Cardansan/CarritoFPV-v1/Piezas Impresión 3D/Imprimir Negro/14.STL

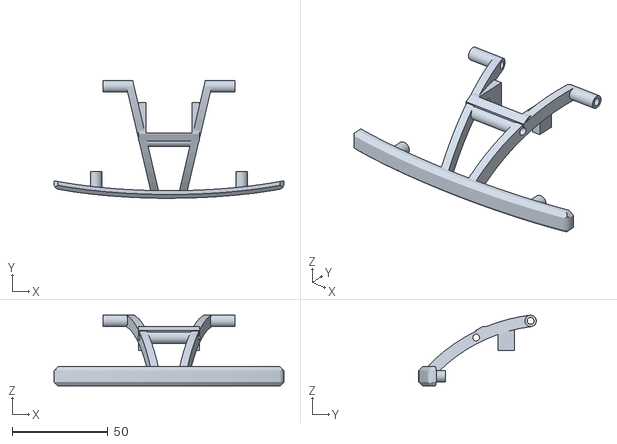
[picture p15: CAD file, 2019-08-24]
Piezas Impresión 3D/Imprimir Negro/14.STL
120.0 x 61.4 x 36.9
