Cardansan/CarritoFPV-v1/Piezas Impresión 3D/Imprimir Negro/9.STL

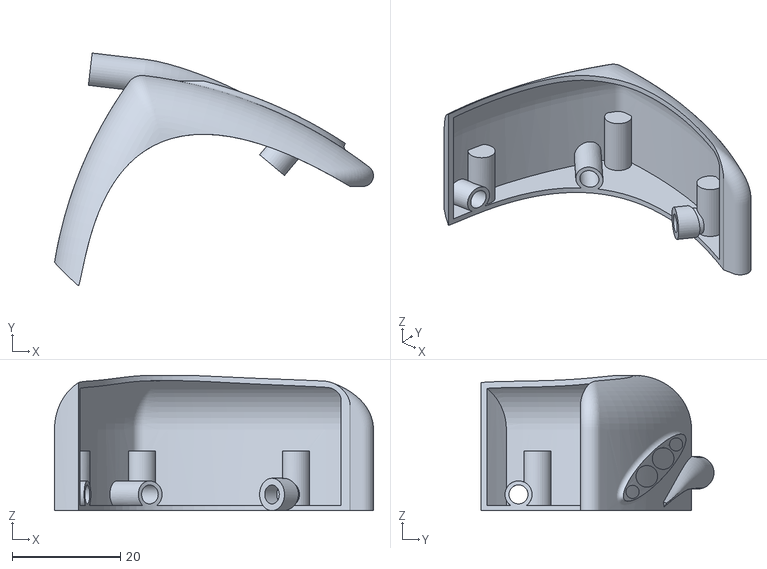
[picture p16: CAD file, 2019-08-24]
Piezas Impresión 3D/Imprimir Negro/9.STL
58.9 x 43.0 x 25.0
