Cardansan/CarritoFPV-v1/Piezas Impresión 3D/Imprimir Negro/19.STL

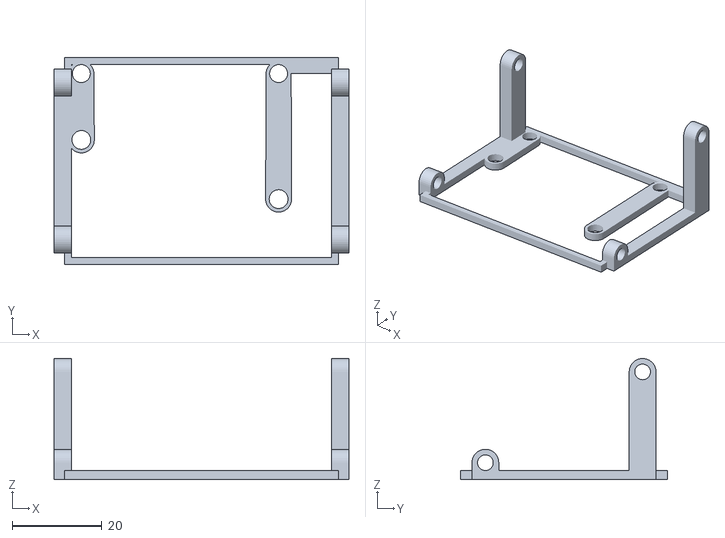
[picture p17: CAD file, 2019-08-24]
Piezas Impresión 3D/Imprimir Negro/19.STL
65.8 x 46.2 x 27.0
