Cardansan/CarritoFPV-v1/Piezas Impresión 3D/Imprimir Negro/10.STL

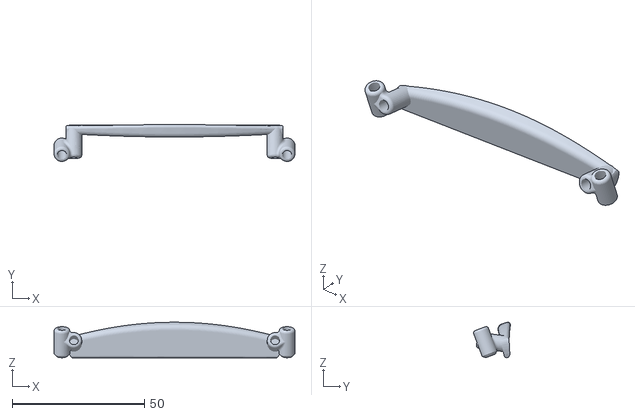
[picture p18: CAD file, 2019-08-24]
Piezas Impresión 3D/Imprimir Negro/10.STL
91.0 x 13.9 x 13.4
